HarryVienna/ESP32-Weather-Station-and-Air-Quality-Monitor/EEZ-Studio-1280x800/images/day_53.png

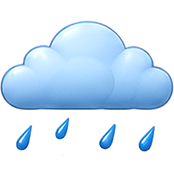
EEZ-Studio-1280x800/images/day_53.png
