HarryVienna/ESP32-Weather-Station-and-Air-Quality-Monitor/EEZ-Studio-1280x800/images/night_1.png

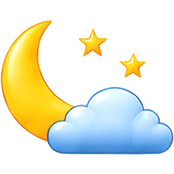
EEZ-Studio-1280x800/images/night_1.png
