HarryVienna/ESP32-Weather-Station-and-Air-Quality-Monitor/Sensor-Receiver/main/main.c

/**
 * @file main.c
 * @brief Sensor Receiver: LoRa + ESP-NOW reception with display and I2C storage
 *
 * Architecture:
 * - LoRa (SX1262): receives sensor data from LoRa sensors
 * - ESP-NOW: receives sensor data from ESP-NOW sensors
 * - Sensor stack: FIFO buffer for I2C readout by the ESP32-P4
 * - Display: OLED 128x64 with scroll function
 */

#include <stdio.h>
#include <string.h>
#include <time.h>
#include "freertos/FreeRTOS.h"
#include "freertos/task.h"
#include "driver/gpio.h"
#include "esp_log.h"
#include "esp_sleep.h"
#include "esp_ota_ops.h"

// Project modules
#include "sensor_stack.h"
#include "display/display.h"
#include "network/lora.h"
#include "network/esp-now.h"
#include "i2c/i2c_slave.h"

/* I2C Slave configuration for P4 Master readout
 * Migrated to network/i2c_slave.c using ESP-IDF I2C Slave Driver v2
 */

static const char* TAG = "MAIN";

#define PIN_VEXT     GPIO_NUM_36  // Display power supply (LOW = on)

// PIN DEFINITIONS FOR RF FRONT-END MODULE (FEM)
#define PIN_VFEM     GPIO_NUM_7   // Amplifier power
#define PIN_PA_CSD   GPIO_NUM_2   // Chip Shut Down / Enable
#define PIN_PA_CPS   GPIO_NUM_46  // RX/TX Path Control

/**
 * @brief Configure VExt, VFem and PA pins
 */
static esp_err_t init_board(void) {
    gpio_config_t io_conf = {
        .pin_bit_mask = (1ULL << PIN_VEXT | 1ULL << PIN_VFEM | 
                         1ULL << PIN_PA_CSD | 1ULL << PIN_PA_CPS),
        .mode = GPIO_MODE_OUTPUT,
        .pull_up_en = GPIO_PULLUP_DISABLE,
        .pull_down_en = GPIO_PULLDOWN_DISABLE,
        .intr_type = GPIO_INTR_DISABLE
    };
    gpio_config(&io_conf);

    // 1. Display on
    gpio_set_level(PIN_VEXT, 0);   // LOW = Turn on display
    ESP_LOGI(TAG, "VExt activated (Display power supply)");

    // 2. Activate amplifier logic
    gpio_set_level(PIN_PA_CSD, 1); 
    gpio_set_level(PIN_PA_CPS, 1); 

    // 3. Amplifier power on
    gpio_set_level(PIN_VFEM, 1); 
    ESP_LOGI(TAG, "VFem activated");

    // Longer delay for stabilization after VExt activation
    vTaskDelay(pdMS_TO_TICKS(200));

    ESP_LOGI(TAG, "Board initialized");
    return ESP_OK;
}

// I2C Slave Register Map (defined in i2c_slave.h)
//   0x00: READ  → Count (1 Byte)
//   0x01: R/W → Packet Read (variable length)
//   0x23: WRITE, 0x01 → Reset Drop-Counter
//   0x24: READ → Total received (4 Byte, uint32_t LE)
//   0x28: READ → Total overwritten (4 Byte, uint32_t LE)

void app_main(void) {
    ESP_LOGI(TAG, "=====================================================");
    ESP_LOGI(TAG, "   Sensor Receiver: LoRa + ESP-NOW                  ");
    ESP_LOGI(TAG, "   Heltec WiFi LoRa 32 ESP32-S3                     ");
    ESP_LOGI(TAG, "=====================================================");

    // Initialize Board (VExt, VFem, PA)
    if (init_board() != ESP_OK) {
        ESP_LOGE(TAG, "Board initialization failed!");
        return;
    }

    // Initialize LoRa Hardware
    if (init_lora() != ESP_OK) {
        ESP_LOGE(TAG, "LoRa initialization failed!");
        return;
    }

        // Initialize WiFi for ESP-NOW
    if (init_wifi() != ESP_OK) {
        ESP_LOGE(TAG, "WiFi initialization failed!");
        return;
    }

    // Initialize display with integrated button for toggle
    if (display_init() != ESP_OK) {
        ESP_LOGE(TAG, "Display initialization with button failed!");
        return;
    }
    
    // Initialize Sensor Stack
    if (sensor_stack_init() != ESP_OK) {
        ESP_LOGE(TAG, "Sensor stack initialization failed!");
        return;
    }
    

    
    // Initialize ESP-NOW
    if (esp_now_start() != ESP_OK) {
        ESP_LOGE(TAG, "ESP-NOW initialization failed!");
        return;
    }
    
    // Start LoRa Receiver (configures SX1262 and starts async RX)
    if (lora_start() != ESP_OK) {
        ESP_LOGE(TAG, "LoRa receiver start failed!");
        return;
    }
    
    // Initialize I2C Slave Interface (for P4 readout + OTA trigger)
    if (i2c_slave_init() != ESP_OK) {
        ESP_LOGW(TAG, "I2C slave init failed (P4 readout unavailable)");
    }

    // Confirms an app installed via OTA as working, otherwise the
    // bootloader rolls back to the previous ota_0/ota_1 partition on the
    // next boot (see CONFIG_BOOTLOADER_APP_ROLLBACK_ENABLE).
    esp_ota_mark_app_valid_cancel_rollback();

    ESP_LOGI(TAG, "Sensor Receiver is running!");
    ESP_LOGI(TAG, "LoRa: Receiving on 868.1 MHz, SF10, BW125");
    ESP_LOGI(TAG, "ESP-NOW: Channel 13, waiting for pairing");
    ESP_LOGI(TAG, "Display: OLED 128x64 SSD1306");
    ESP_LOGI(TAG, "I2C: Slave mode for P4 readout");
    
    // Main loop - everything runs via callbacks
    while (1) {
        vTaskDelay(pdMS_TO_TICKS(1000));
    }
}
