HarryVienna/ESP32-Weather-Station-and-Air-Quality-Monitor/Sensor-Receiver/main/lora/lora_receiver.c

#include "lora_receiver.h"
#include "sensor_stack.h"
#include "display_driver.h"
#include "esp_log.h"

static const char* TAG = "lora_rx";

static volatile uint32_t g_packets_received = 0;
static volatile uint32_t g_crc_errors = 0;

/* ============================================================================
 * Helper: sensor_type_to_string
 * ============================================================================ */

static const char* sensor_type_to_string(uint8_t type) {
    switch (type) {
        case SENSOR_TYPE_BME280:  return "BME280";
        case SENSOR_TYPE_HDC1080: return "HDC1080";
        case SENSOR_TYPE_DHT22:   return "DHT22";
        case SENSOR_TYPE_WIND:    return "WIND";
        case SENSOR_TYPE_RAIN:    return "RAIN";
        case SENSOR_TYPE_LIGHT:   return "LIGHT";
        case SENSOR_TYPE_CUSTOM:  return "CUSTOM";
        default:                  return "???";
    }
}

/* ============================================================================
 * SX1262 Receive Callback
 * ============================================================================ */

static void lora_rx_callback(uint8_t *data, uint8_t len, sx1262_packet_status_t *status) {
    if (data == NULL || len == 0 || status == NULL) {
        return;
    }
    
    // Minimum size: header (4) + link metadata (12) = 16 bytes, no payload
    if (len < sizeof(packet_header_t) + sizeof(link_metadata_t)) {
        ESP_LOGW(TAG, "Packet too small: expected >= %zu, got %d", 
                 sizeof(packet_header_t) + sizeof(link_metadata_t), len);
        g_crc_errors++;
        return;
    }
    
    // Parse header to get payload length
    packet_header_t *header = (packet_header_t *)data;
    uint8_t expected_total = sizeof(packet_header_t) + sizeof(link_metadata_t) + header->payload_len;
    
    if (len != expected_total) {
        ESP_LOGW(TAG, "Packet size mismatch: expected %d, got %d", expected_total, len);
        g_crc_errors++;
        return;
    }
    
    if (header->payload_len > MAX_PAYLOAD_SIZE) {
        ESP_LOGW(TAG, "Payload too large: %d bytes (max %d)", 
                 header->payload_len, MAX_PAYLOAD_SIZE);
        g_crc_errors++;
        return;
    }
    
    // Build sensor_packet_t from received data
    sensor_packet_t packet;
    
    // Copy header
    memcpy(&packet.header, data, sizeof(packet_header_t));
    
    // Copy link metadata (starts after header)
    memcpy(&packet.link, data + sizeof(packet_header_t), sizeof(link_metadata_t));
    
    // Add LoRa-specific metadata (override any sender values)
    packet.link.msg_source = SENSOR_SOURCE_LORA;
    packet.link.lora_rssi = status->rssi_pkt;
    packet.link.lora_snr = status->snr_pkt;
    packet.link.timestamp = xTaskGetTickCount();
    
    // Copy payload (starts after header + link metadata)
    uint8_t *payload_start = data + sizeof(packet_header_t) + sizeof(link_metadata_t);
    memcpy(packet.payload, payload_start, header->payload_len);
    
    // Push to stack
    esp_err_t ret = sensor_stack_push(&packet, SENSOR_SOURCE_LORA);
    if (ret == ESP_OK) {
        g_packets_received++;
        
        // Update display (only needs header + link metadata)
        display_driver_update(&packet);
        
        // Log every 10th packet
        if (g_packets_received % 10 == 0) {
            ESP_LOGI(TAG, "LoRa RX #%lu: Sensor %d [%s] payload=%d, RSSI:%d, SNR:%.1f, Stack:%d",
                     g_packets_received, packet.header.sensor_nr,
                     sensor_type_to_string(packet.header.sensor_type),
                     packet.header.payload_len,
                     status->rssi_pkt, status->snr_pkt,
                     sensor_stack_count());
        }
    } else {
        ESP_LOGW(TAG, "Stack full, LoRa packet dropped");
    }
}

/* ============================================================================
 * API Functions
 * ============================================================================ */

esp_err_t lora_receiver_init(void) {
    g_packets_received = 0;
    g_crc_errors = 0;
    return ESP_OK;
}

esp_err_t lora_receiver_start(void) {
    sx1262_config_t config = {
        .modem_mode = SX1262_MODEM_LORA,
        .frequency = LORA_FREQUENCY,
        .tx_power = LORA_TX_POWER,
        .bandwidth = LORA_BANDWIDTH,
        .spreading_factor = LORA_SPREADING_FACTOR,
        .coding_rate = LORA_CODING_RATE,
        .preamble_length = LORA_PREAMBLE_LENGTH,
        .payload_length = LORA_PAYLOAD_LENGTH,
        .crc_on = LORA_CRC_ON,
        .iq_inverted = LORA_IQ_INVERTED,
        .rx_gain_boosted = LORA_RX_GAIN_BOOSTED,
        .sync_word = 0x1424,  // Public LoRa network
    };
    
    ESP_LOGI(TAG, "Configuring LoRa: %lu MHz, SF%d, BW%d",
             config.frequency / 1000000, config.spreading_factor,
             (config.bandwidth == LORA_BW_125) ? 125 :
             (config.bandwidth == LORA_BW_250) ? 250 : 500);
    
    esp_err_t ret = sx1262_configure(&config);
    if (ret != ESP_OK) {
        ESP_LOGE(TAG, "Failed to configure LoRa: %s", esp_err_to_name(ret));
        return ret;
    }
    
    // Start async receive with callback
    ret = sx1262_start_receive_async(lora_rx_callback);
    if (ret != ESP_OK) {
        ESP_LOGE(TAG, "Failed to start async RX: %s", esp_err_to_name(ret));
        return ret;
    }
    
    ESP_LOGI(TAG, "LoRa receiver started");
    return ESP_OK;
}

void lora_receiver_stop(void) {
    sx1262_stop_receive_async();
    ESP_LOGI(TAG, "LoRa receiver stopped");
}

void lora_receiver_stats(uint32_t *packets_received, uint32_t *crc_errors) {
    if (packets_received) *packets_received = g_packets_received;
    if (crc_errors) *crc_errors = g_crc_errors;
}
